derekfountain/zx-spectrum-pico-interface-one/images/case_offset.jpg

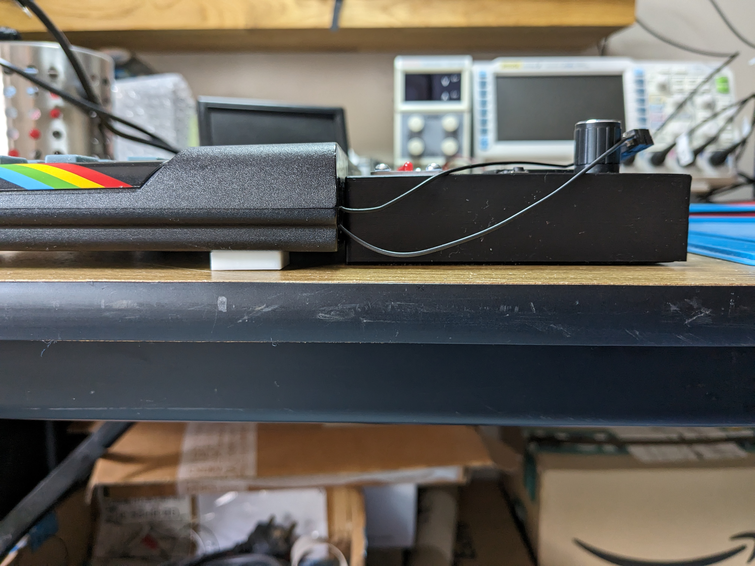
images/case_offset.jpg
