derekfountain/zx-spectrum-pico-interface-one/images/cat1_1633_2_2byte_ins_starts.png

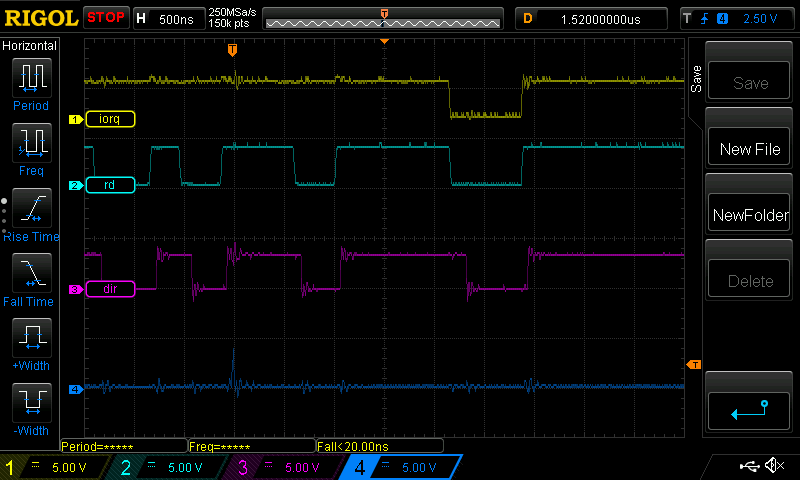
images/cat1_1633_2_2byte_ins_starts.png
