derekfountain/zx-spectrum-pico-interface-one/images/cat1_1633_3_14uSecsbetweenINIRS.png

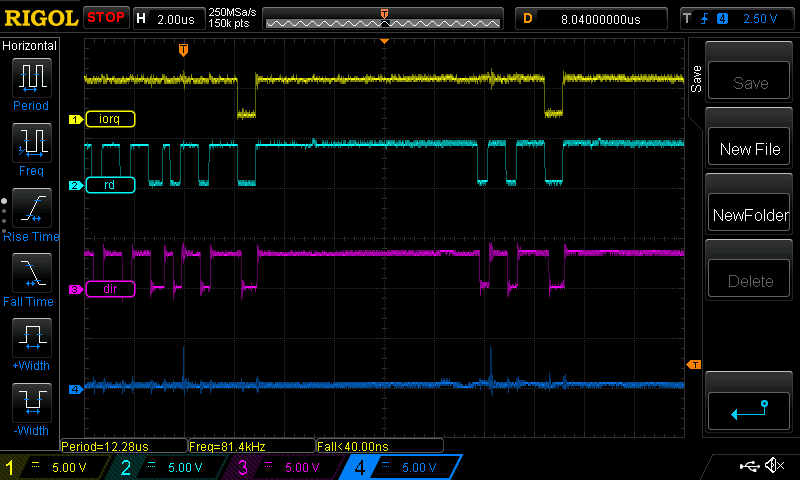
images/cat1_1633_3_14uSecsbetweenINIRS.png
