derekfountain/zx-spectrum-pico-interface-one/images/cat1_1633_4_finalINIR.png

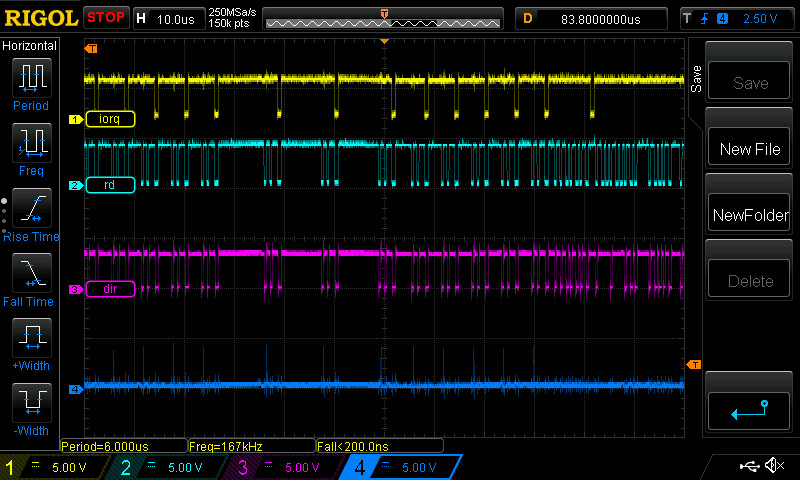
images/cat1_1633_4_finalINIR.png
