derekfountain/zx-spectrum-pico-interface-one/images/cat1_1633_finalOUT.png

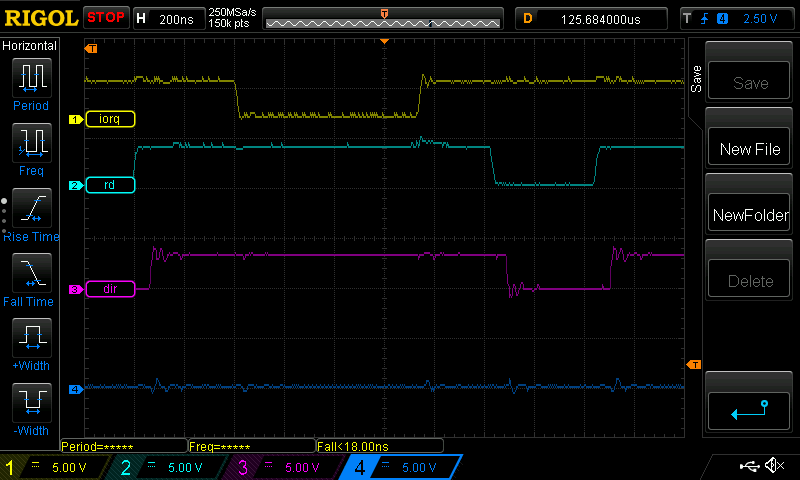
images/cat1_1633_finalOUT.png
