derekfountain/zx-spectrum-pico-interface-one/images/cat1_1633_pastFinalOUT.png

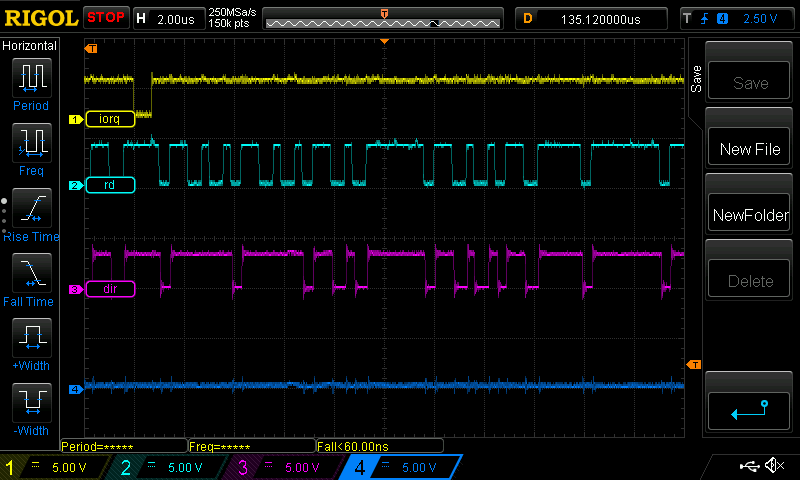
images/cat1_1633_pastFinalOUT.png
