derekfountain/zx-spectrum-pico-interface-one/images/cat1_1633_pastFinalOUTDetail.png

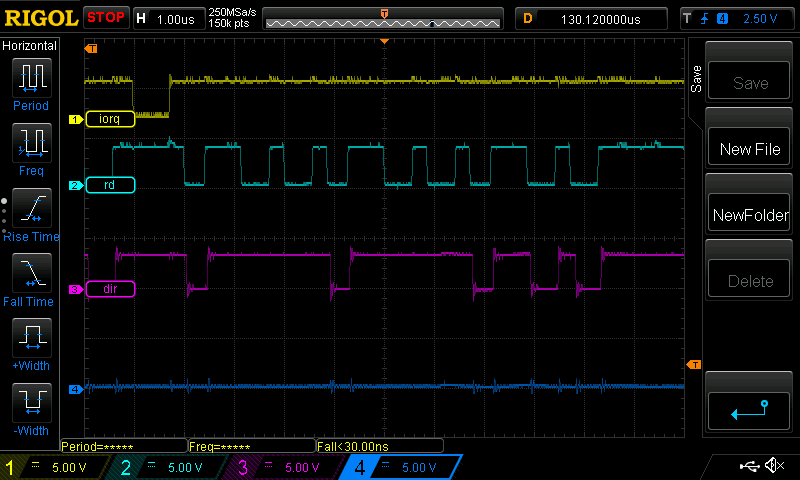
images/cat1_1633_pastFinalOUTDetail.png
