derekfountain/zx-spectrum-pico-interface-one/images/gui_screen.jpg

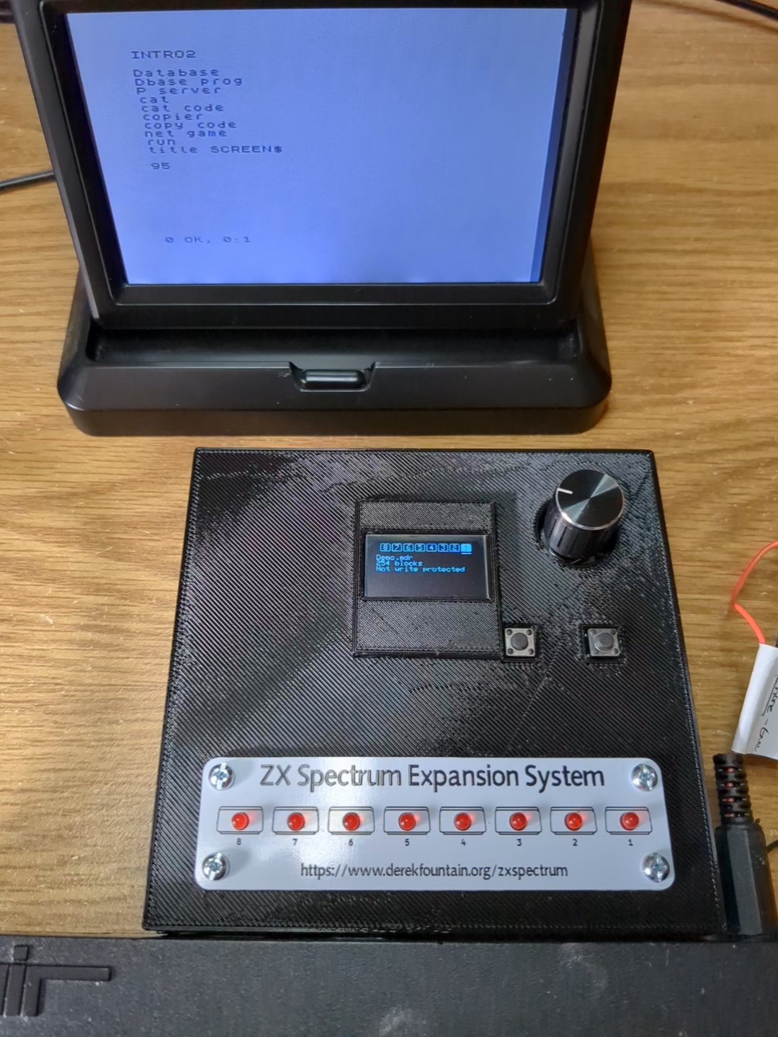
images/gui_screen.jpg
