derekfountain/zx-spectrum-pico-interface-one/images/if1_board_v10.jpg

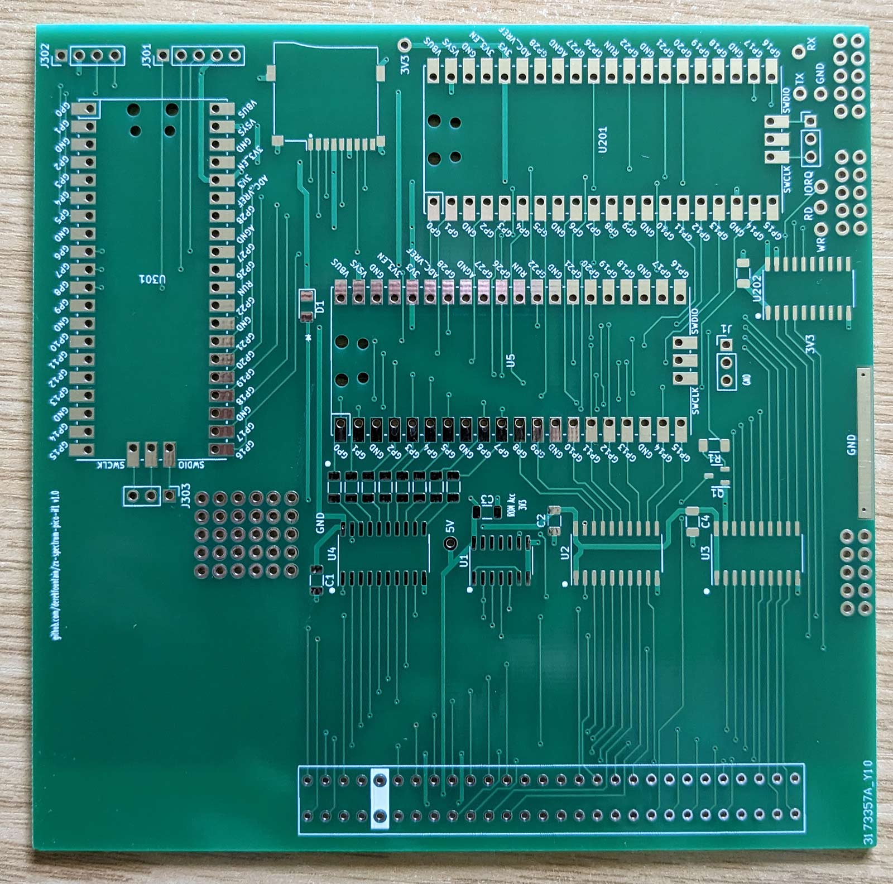
images/if1_board_v10.jpg
