derekfountain/zx-spectrum-pico-interface-one/images/lower_board.jpg

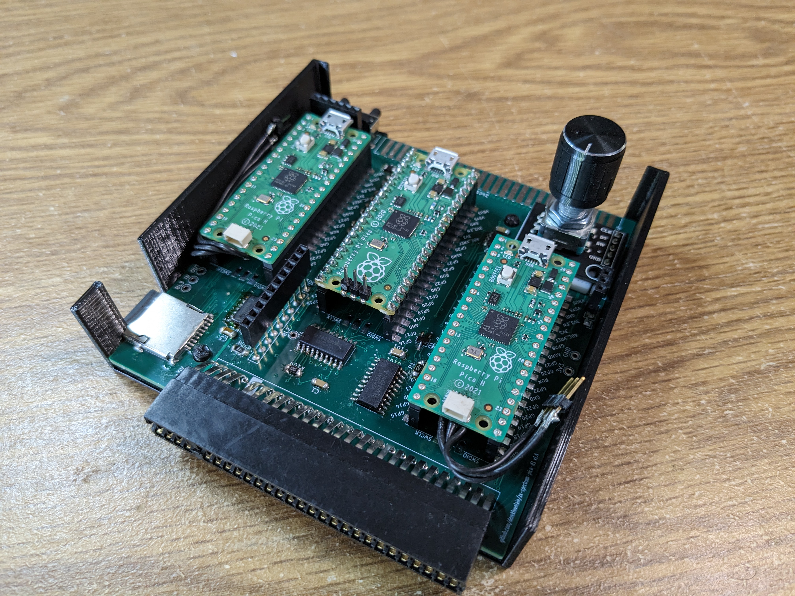
images/lower_board.jpg
