derekfountain/zx-spectrum-pico-interface-one/images/lower_board_rear.jpg

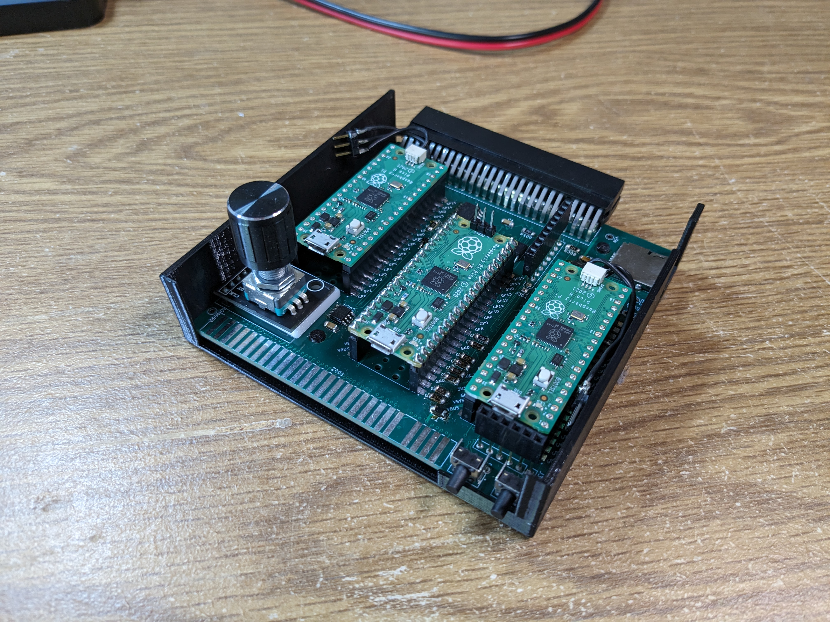
images/lower_board_rear.jpg
