derekfountain/zx-spectrum-pico-interface-one/images/non-working-board.jpg

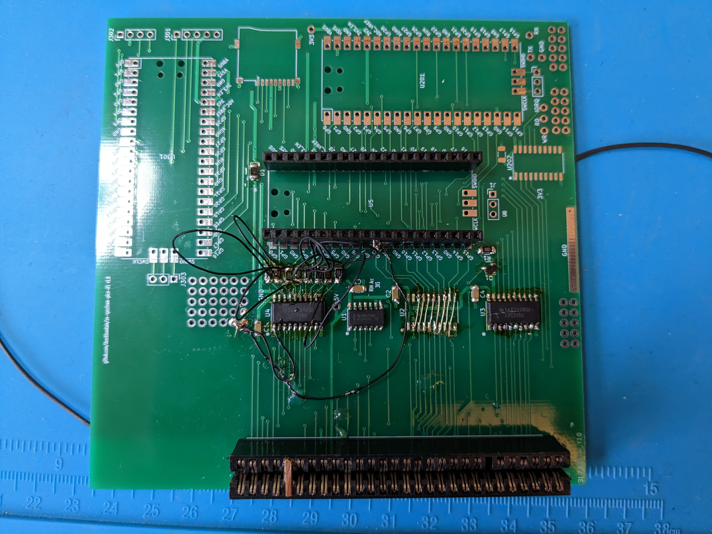
images/non-working-board.jpg
