derekfountain/zx-spectrum-pico-interface-one/images/picos1.jpg

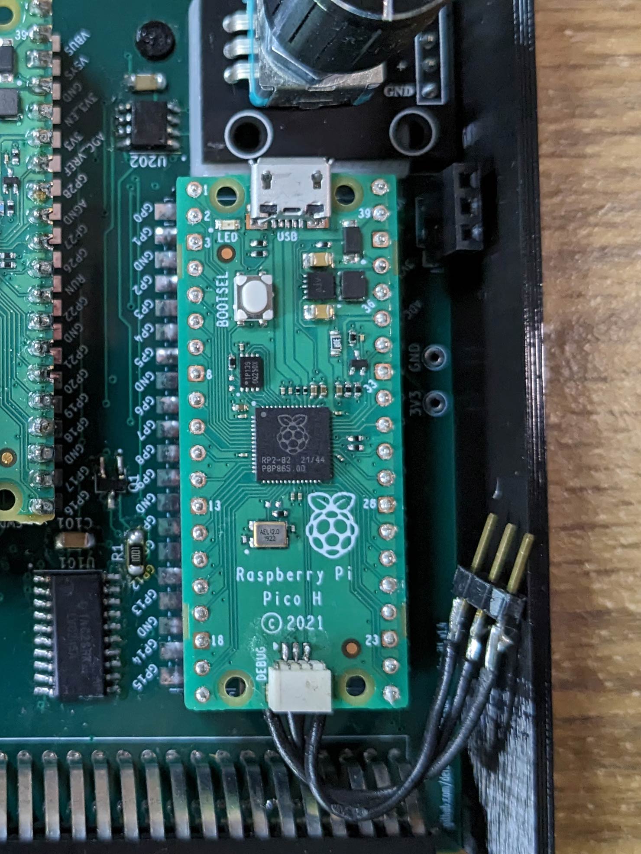
images/picos1.jpg
