derekfountain/zx-spectrum-pico-interface-one/images/picos2.jpg

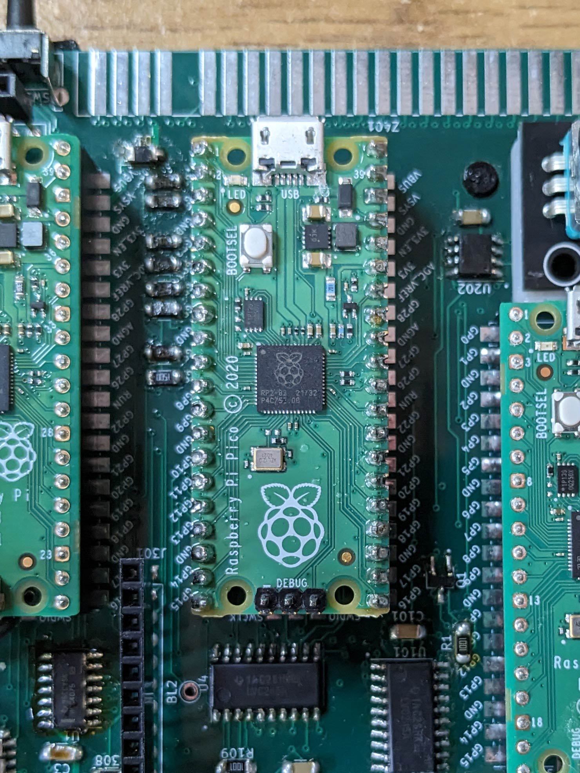
images/picos2.jpg
