derekfountain/zx-spectrum-pico-interface-one/images/picos3.jpg

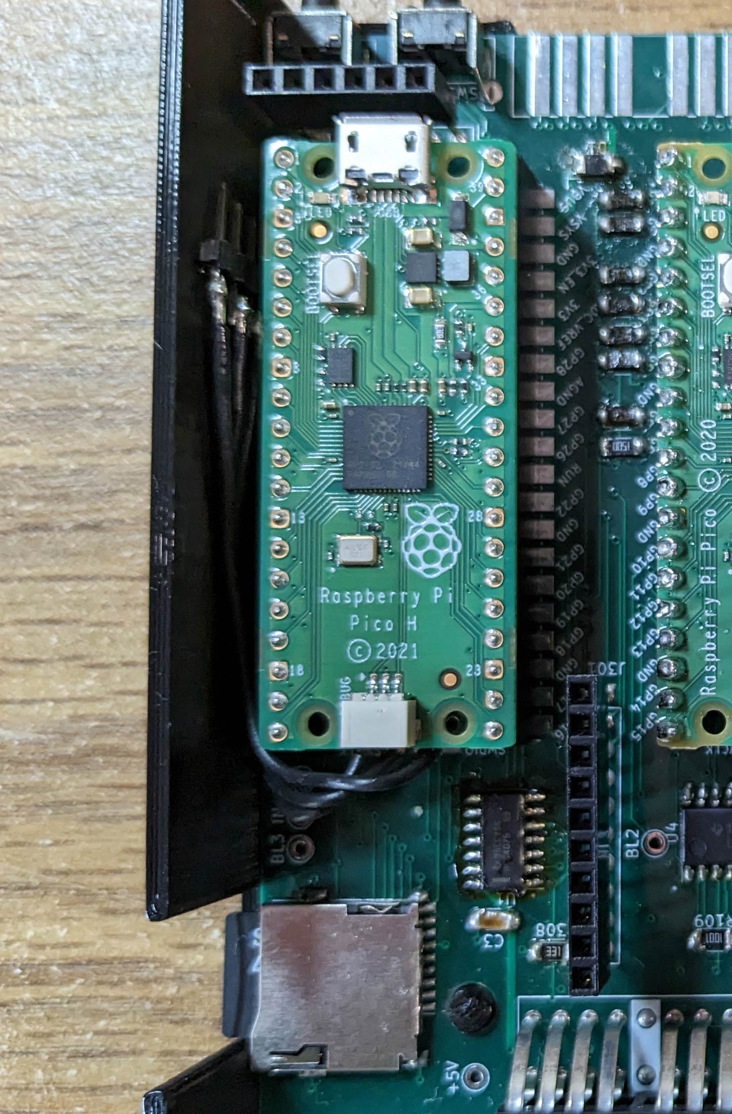
images/picos3.jpg
