derekfountain/zx-spectrum-pico-interface-one/images/pio_io_read.png

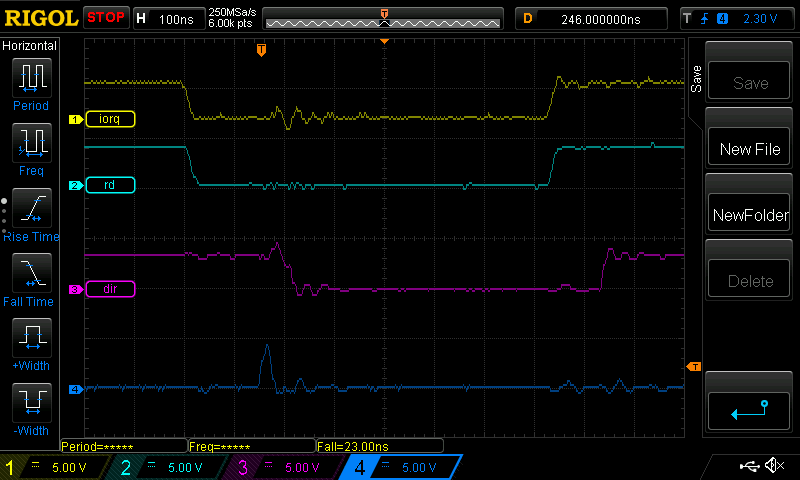
images/pio_io_read.png
