derekfountain/zx-spectrum-pico-interface-one/images/pio_rom_read.png

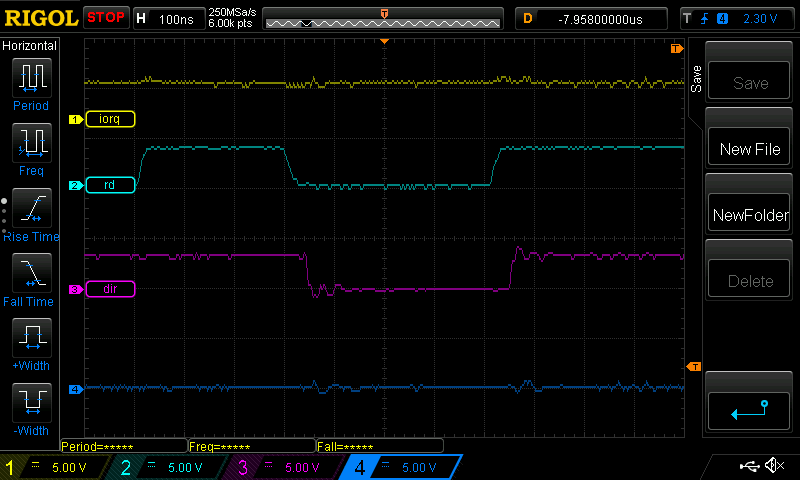
images/pio_rom_read.png
