derekfountain/zx-spectrum-pico-interface-one/images/prototype2_gui.jpg

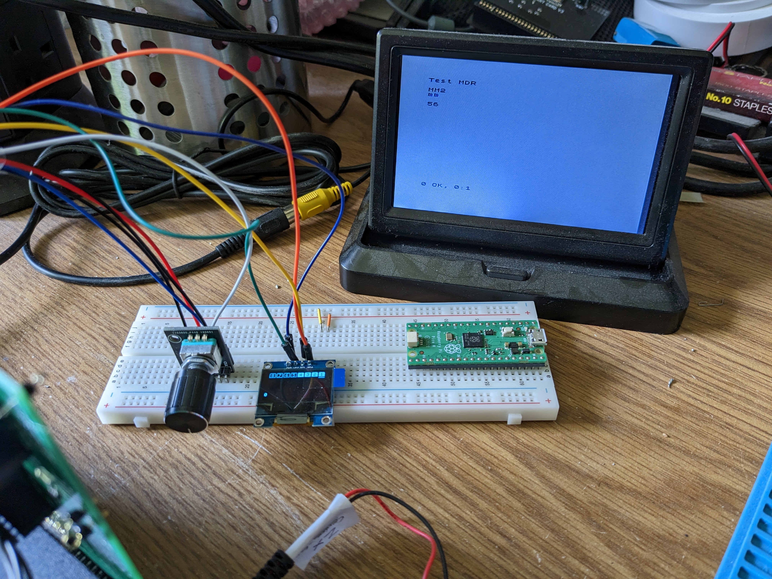
images/prototype2_gui.jpg
