derekfountain/zx-spectrum-pico-interface-one/images/PXL_20230621_114636137.jpg

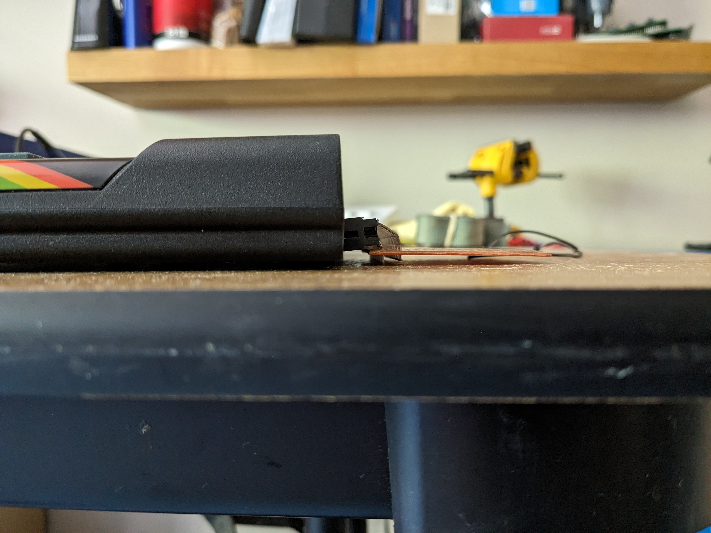
images/PXL_20230621_114636137.jpg
