derekfountain/zx-spectrum-pico-interface-one/images/PXL_20230621_114655089.jpg

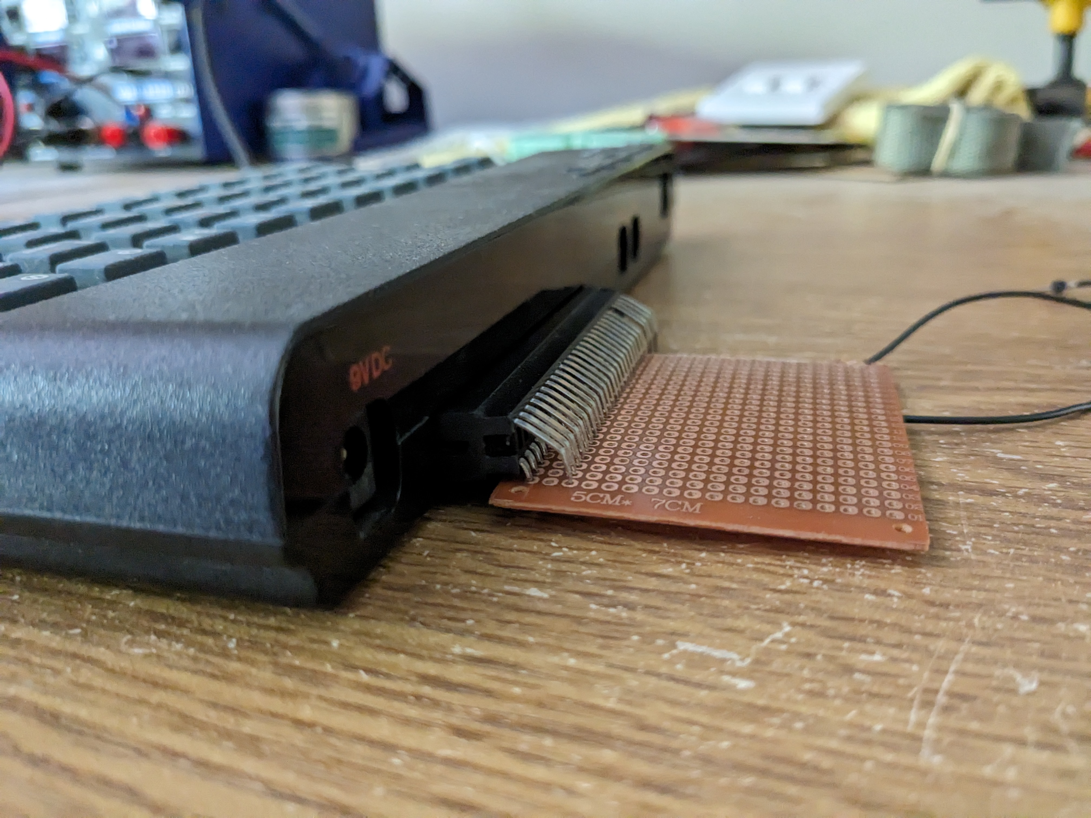
images/PXL_20230621_114655089.jpg
