derekfountain/zx-spectrum-pico-interface-one/images/spi_on_board.jpg

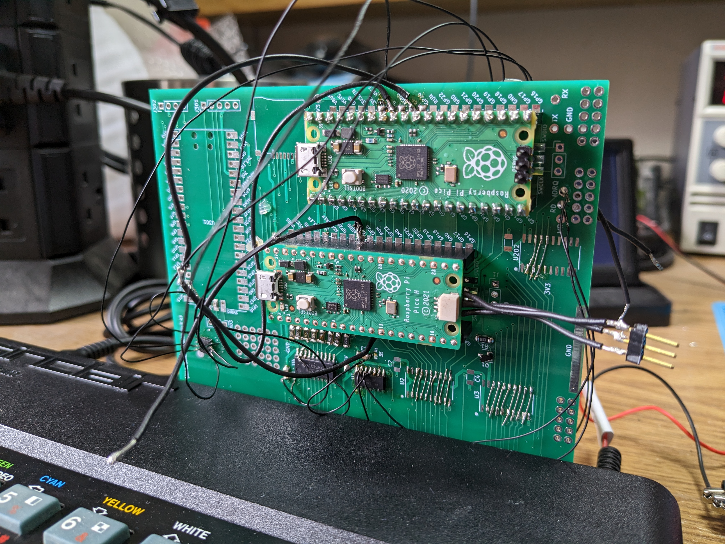
images/spi_on_board.jpg
