derekfountain/zx-spectrum-pico-interface-one/images/spi_ram_prototype.jpg

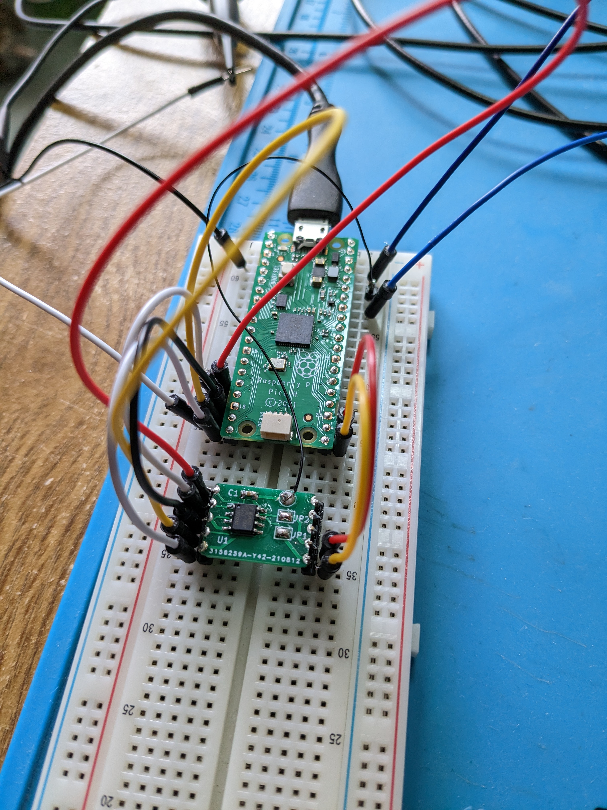
images/spi_ram_prototype.jpg
