derekfountain/zx-spectrum-pico-interface-one/images/spi_read_3us.png

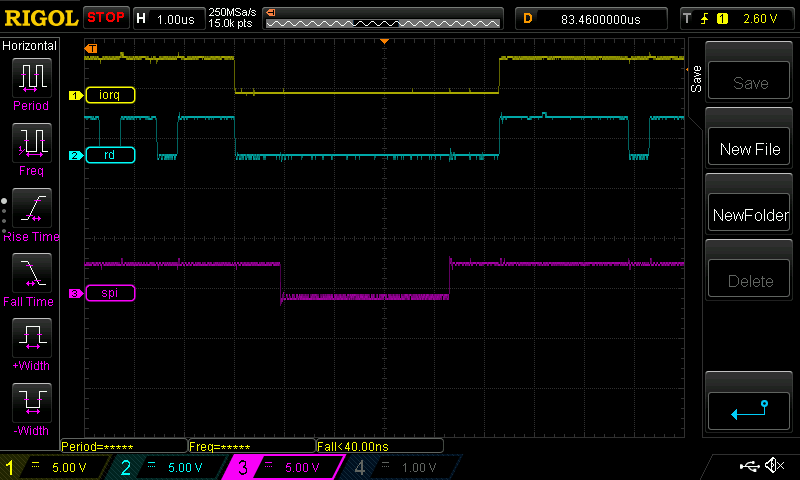
images/spi_read_3us.png
