derekfountain/zx-spectrum-pico-interface-one/images/top_board.jpg

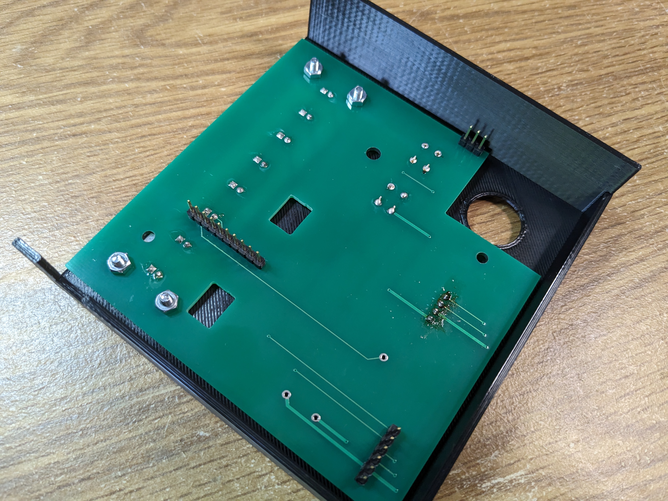
images/top_board.jpg
