derekfountain/zx-spectrum-pico-interface-one/images/trace_first_write_fails_needs_copy_to_ram.png

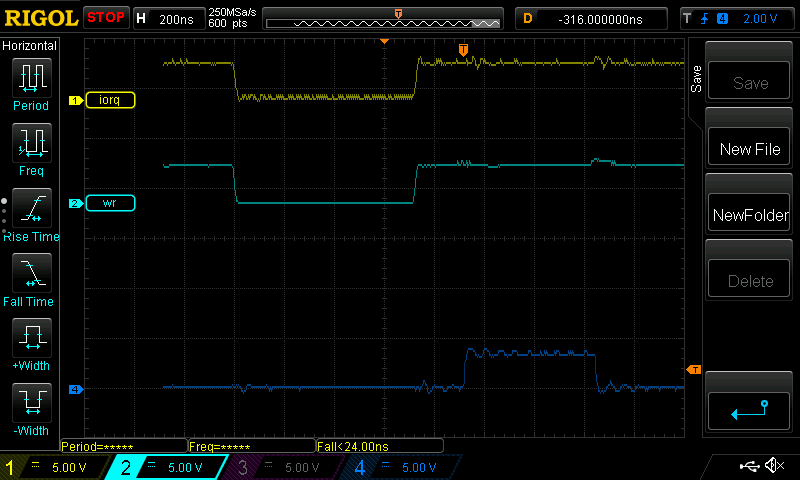
images/trace_first_write_fails_needs_copy_to_ram.png
