derekfountain/zx-spectrum-pico-interface-one/images/trace_second_write_ok.png

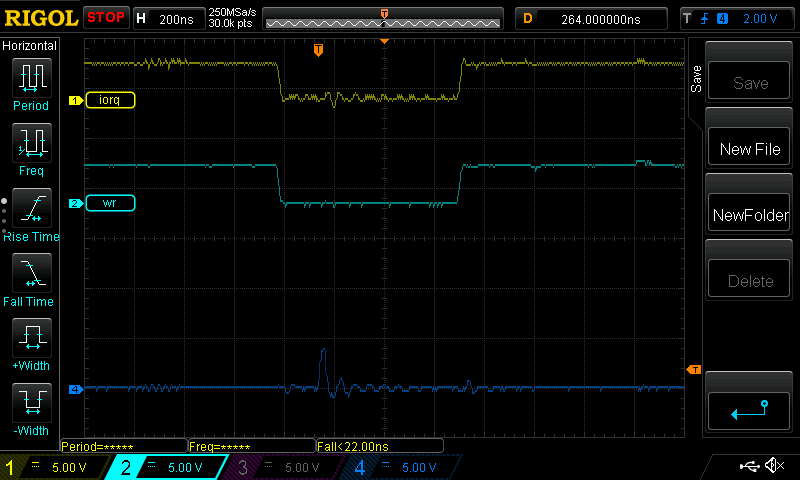
images/trace_second_write_ok.png
