derekfountain/zx-spectrum-pico-interface-one/images/trace_write_e7.png

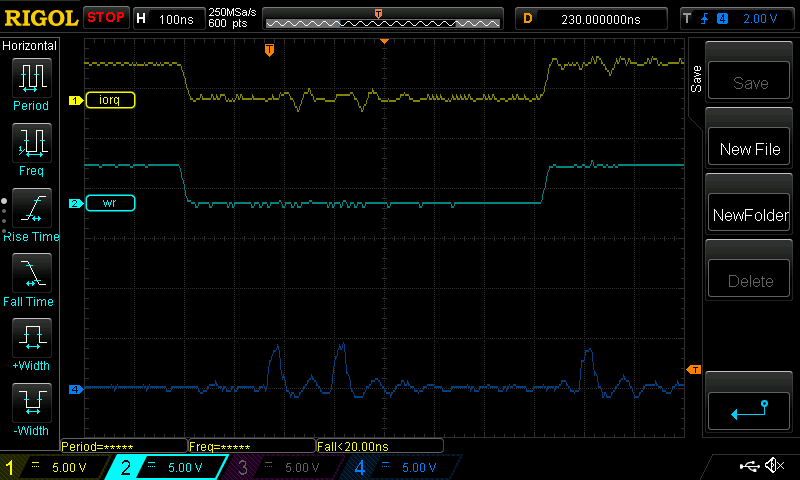
images/trace_write_e7.png
