derekfountain/zx-spectrum-pico-interface-one/images/two_boards.jpg

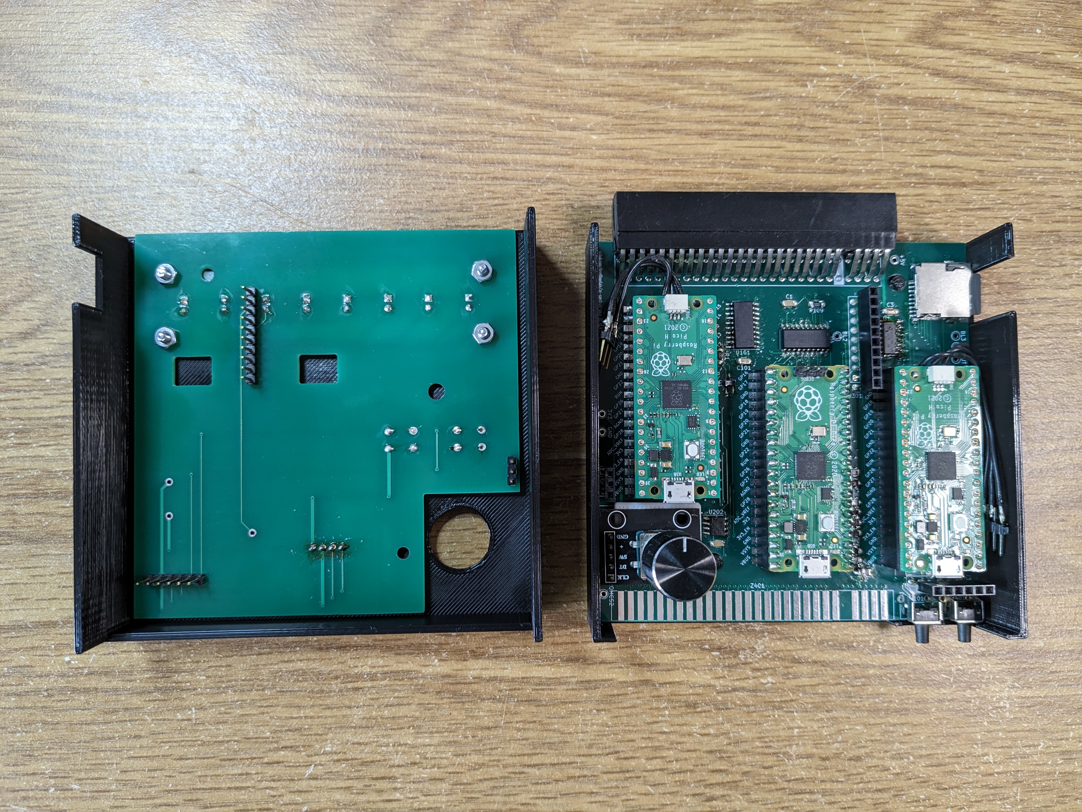
images/two_boards.jpg
