derekfountain/zx-spectrum-pico-interface-one/images/two_picos.jpg

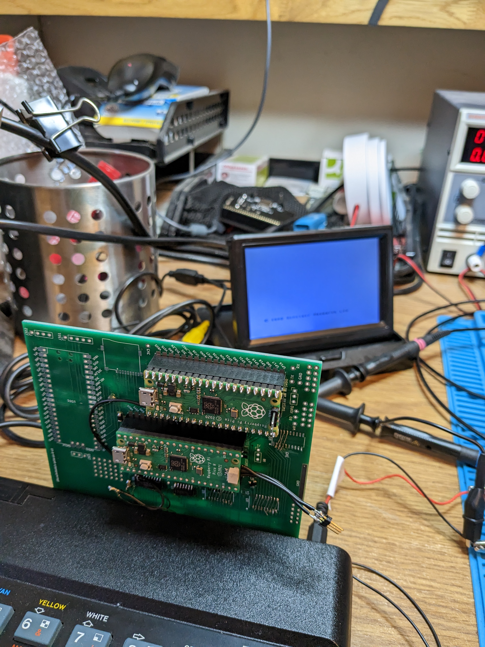
images/two_picos.jpg
