derekfountain/zx-spectrum-pico-interface-one/images/wait_in_read.png

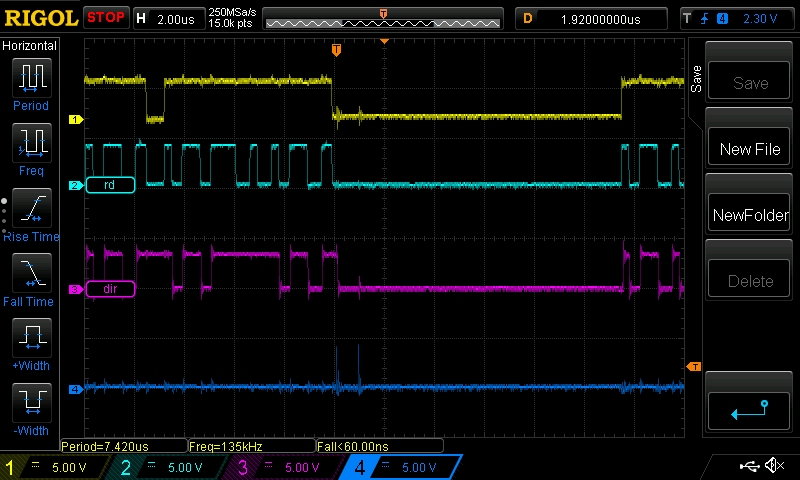
images/wait_in_read.png
