derekfountain/zx-spectrum-pico-interface-one/images/zses_1.jpg

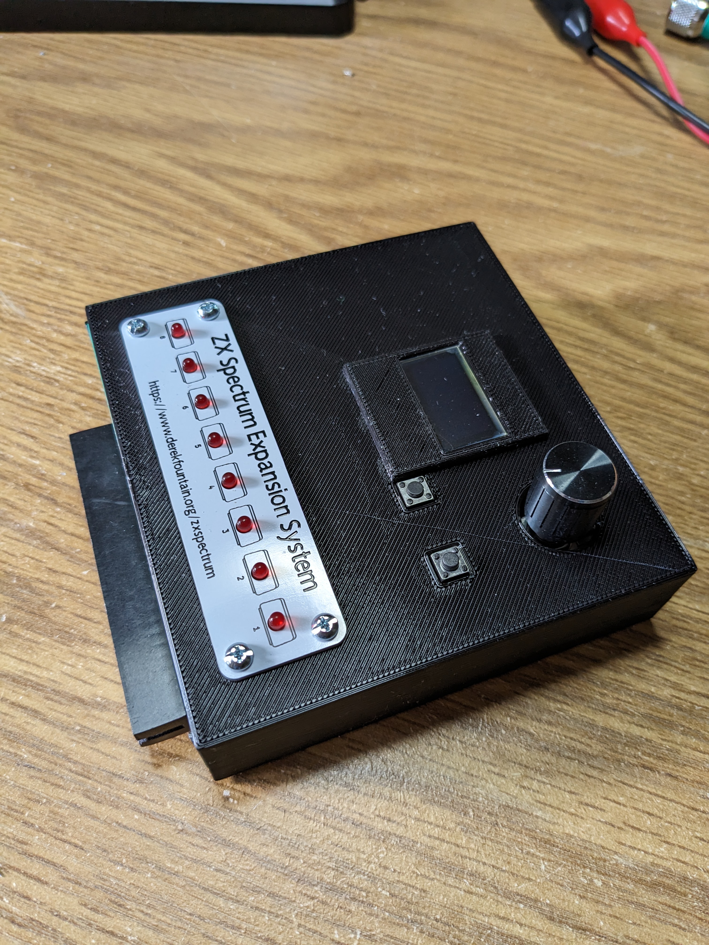
images/zses_1.jpg
