derekfountain/zx-spectrum-pico-interface-one/images/zses_v1_1.jpg

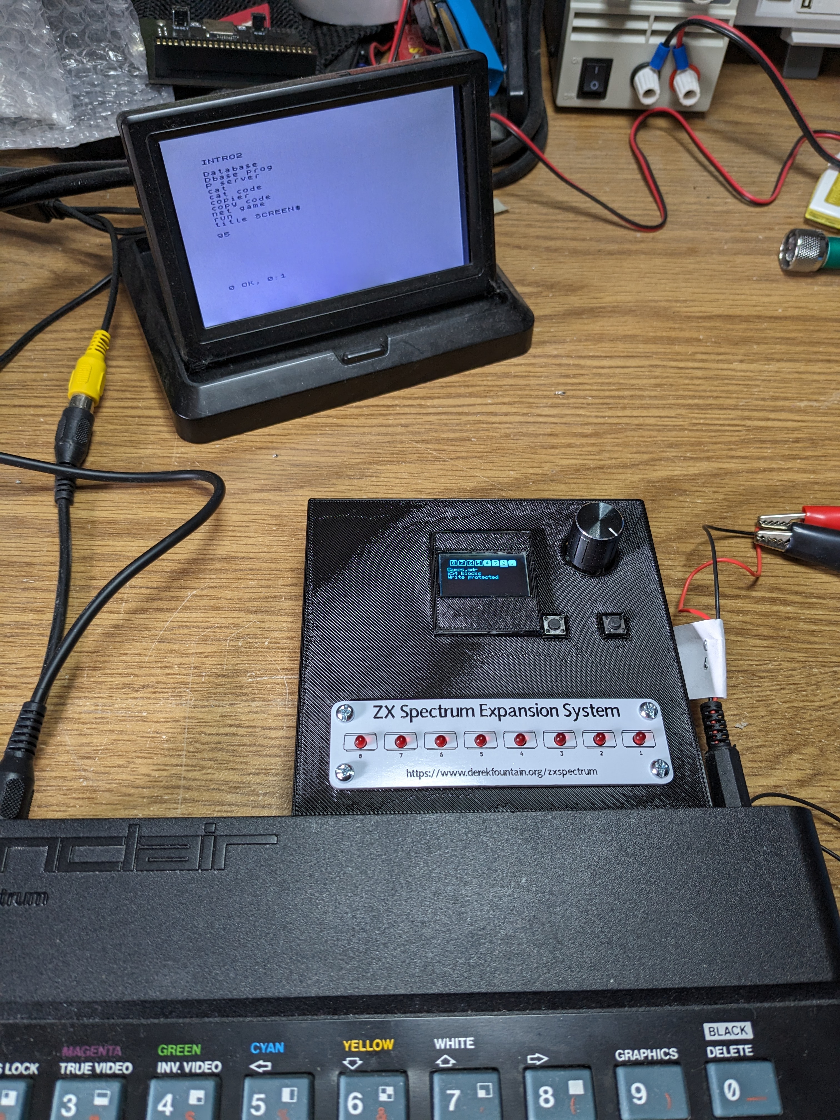
images/zses_v1_1.jpg
