derekfountain/zx-spectrum-pico-interface-one/images/zx_feet_spacers.jpg

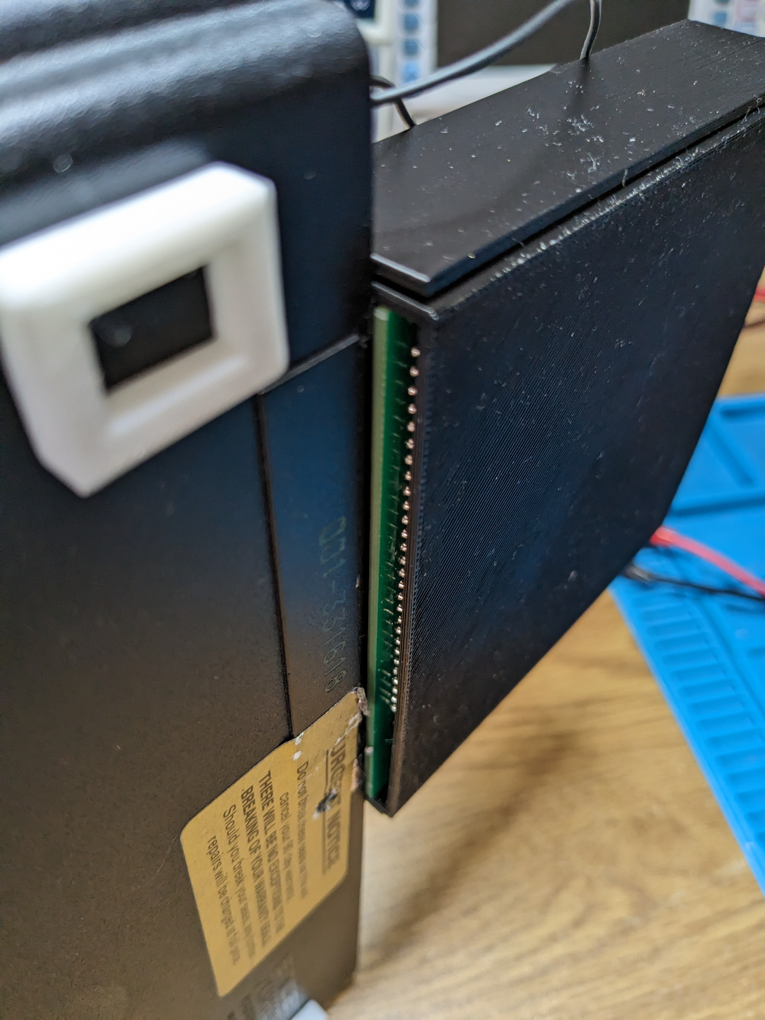
images/zx_feet_spacers.jpg
