derekfountain/zx-spectrum-pico-interface-one/3d_print/pcb_sandwich_spacer/pcb_spacer.scad

cube([20, 18, 4]); 
