derekfountain/zx-spectrum-pico-interface-one/3d_print/top_panel/mII.png

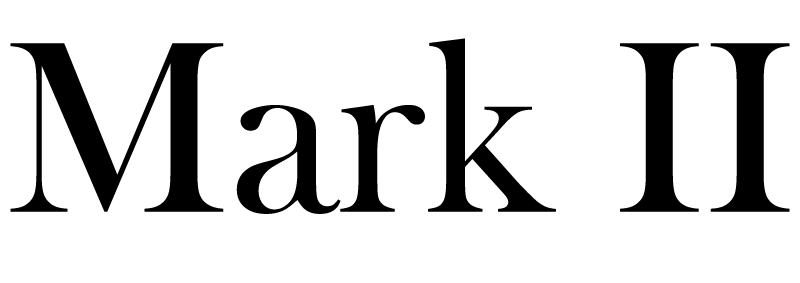
3d_print/top_panel/mII.png
