derekfountain/zx-spectrum-pico-interface-one/images/oled_encoder_wiring_prototype2.jpg

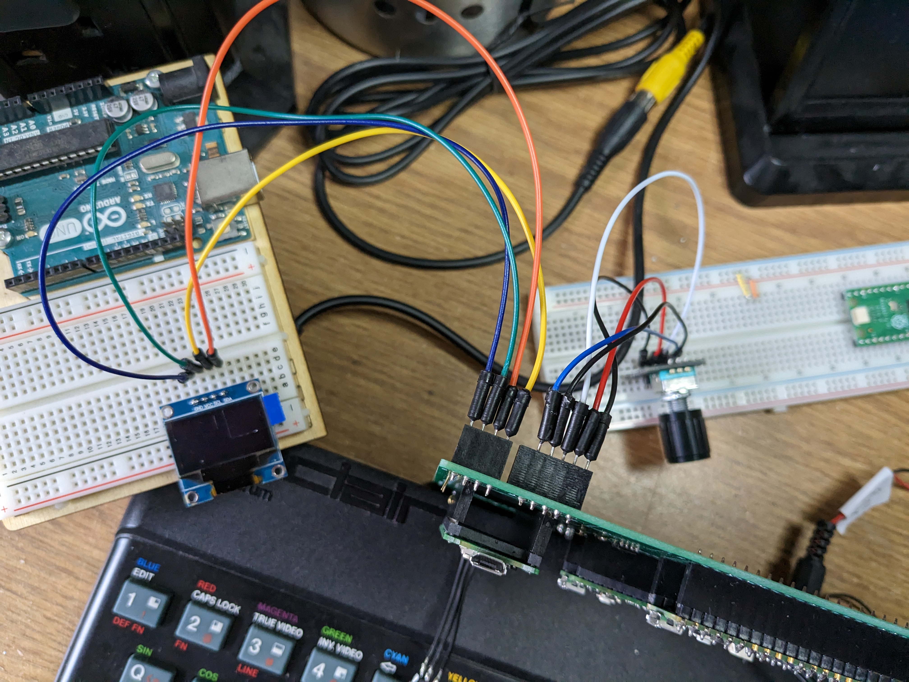
images/oled_encoder_wiring_prototype2.jpg
