derekfountain/zx-spectrum-pico-interface-one/firmware-io/zx_pico_if1_io_fw.c

/*
 * ZX Pico IF1 Firmware, a Raspberry Pi Pico based ZX Interface One emulator
 * Copyright (C) 2023 Derek Fountain
 * 
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
 * You should have received a copy of the GNU General Public License
 * along with this program; if not, write to the Free Software
 * Foundation, Inc., 51 Franklin Street, Fifth Floor, Boston, MA  02110-1301, USA.
 */

/*
 * cmake -DCMAKE_BUILD_TYPE=Debug ..
 * make -j10
 * sudo openocd -f interface/picoprobe.cfg -f target/rp2040.cfg -c "program ./zx_pico_if1_io_fw.elf verify reset exit"
 * sudo openocd -f interface/picoprobe.cfg -f target/rp2040.cfg
 * gdb-multiarch ./zx_pico_if1_io_fw.elf
 *  target remote localhost:3333
 *  load
 *  monitor reset init
 *  continue
 */

#include <stdio.h>
#include <stdint.h>
#include <string.h>
#include <stdlib.h>
#include "pico/stdlib.h"
#include "hardware/gpio.h"
#include "pico/binary_info.h"
#include "pico/multicore.h"
#include "pico/platform.h"
#include "hardware/timer.h"
#include "hardware/spi.h"

#include "if1.h"
#include "spi.h"
#include "ui_io_comms.h"
#include "cartridge.h"

#include "hardware/pio.h"
#include "hardware/clocks.h"
#include "mreq_dir.pio.h"

/* Link to IO Pico is done with transputer based PIO code */
#include "picoputer.pio.h"
#include "link_common.h"

const uint8_t LINKOUT_PIN     = 12;
const uint8_t LINKIN_PIN      = 13;

/* UI to IO Pico link state machines */
static int linkout_sm;
static int linkin_sm;

/* 1 instruction on the 133MHz microprocessor is 7.5ns */
/* 1 instruction on the 140MHz microprocessor is 7.1ns */
/* 1 instruction on the 150MHz microprocessor is 6.6ns */
/* 1 instruction on the 200MHz microprocessor is 5.0ns */

#define OVERCLOCK 150000
//#define OVERCLOCK 270000

const uint8_t LED_PIN = PICO_DEFAULT_LED_PIN;

/*
 * The IF1 port signal comes from the ROM Pico which has can see the
 * address lines. When that's active (low) the Z80 has 0xEF or 0xE7
 * on the lower address lines. The extra bit is A3 which this Pico
 * still needs to be able to see to differentiate them
 */
const uint8_t  IF1_PORT_SIGNAL_GP         = 8;
const uint8_t  A3_GP                      = 9;

const uint32_t IF1_PORT_SIGNAL_BIT_MASK = ((uint32_t)1 <<  IF1_PORT_SIGNAL_GP);
const uint32_t A3_BIT_MASK              = ((uint32_t)1 <<  A3_GP);

const uint8_t  D0_GP        = 0;
const uint8_t  D1_GP        = 1;
const uint8_t  D2_GP        = 2;
const uint8_t  D3_GP        = 3; 
const uint8_t  D4_GP        = 4;
const uint8_t  D5_GP        = 5;
const uint8_t  D6_GP        = 6;
const uint8_t  D7_GP        = 7;

const uint32_t D0_BIT_MASK  = ((uint32_t)1 <<  D0_GP);
const uint32_t D1_BIT_MASK  = ((uint32_t)1 <<  D1_GP);
const uint32_t D2_BIT_MASK  = ((uint32_t)1 <<  D2_GP);
const uint32_t D3_BIT_MASK  = ((uint32_t)1 <<  D3_GP);
const uint32_t D4_BIT_MASK  = ((uint32_t)1 <<  D4_GP);
const uint32_t D5_BIT_MASK  = ((uint32_t)1 <<  D5_GP);
const uint32_t D6_BIT_MASK  = ((uint32_t)1 <<  D6_GP);
const uint32_t D7_BIT_MASK  = ((uint32_t)1 <<  D7_GP);

const uint32_t DBUS_MASK    = ((uint32_t)1 << D0_GP) |
                              ((uint32_t)1 << D1_GP) |
                              ((uint32_t)1 << D2_GP) |
                              ((uint32_t)1 << D3_GP) |
                              ((uint32_t)1 << D4_GP) |
                              ((uint32_t)1 << D5_GP) |
                              ((uint32_t)1 << D6_GP) |
                              ((uint32_t)1 << D7_GP);

/* Input from Z80 indicating an I/O request is happening */
const uint8_t  IORQ_GP                  = 20;
const uint32_t IORQ_BIT_MASK            = ((uint32_t)1 << IORQ_GP);

const uint8_t  RD_GP                    = 21;
const uint32_t RD_BIT_MASK              = ((uint32_t)1 << RD_GP);

const uint8_t  WR_GP                    = 22;
const uint32_t WR_BIT_MASK              = ((uint32_t)1 << WR_GP);

/*
 * These are the bits which allow us to decide whether what is
 * on the Z80 buses is IF1 related
 */
const uint32_t IF1_IOPORT_ACCESS_BIT_MASK = IORQ_BIT_MASK |
                                            RD_BIT_MASK |
                                            WR_BIT_MASK |
                                            IF1_PORT_SIGNAL_BIT_MASK |
                                            A3_BIT_MASK;

const uint32_t PORT_E7_READ =  ((uint32_t)0 << IORQ_GP) |
                               ((uint32_t)0 << RD_GP)   |
                               ((uint32_t)1 << WR_GP)   |
                               ((uint32_t)0 << IF1_PORT_SIGNAL_GP)   |
                               ((uint32_t)0 << A3_GP);

const uint32_t PORT_EF_READ =  ((uint32_t)0 << IORQ_GP) |
                               ((uint32_t)0 << RD_GP)   |
                               ((uint32_t)1 << WR_GP)   |
                               ((uint32_t)0 << IF1_PORT_SIGNAL_GP)   |
                               ((uint32_t)1 << A3_GP);

const uint32_t PORT_E7_WRITE = ((uint32_t)0 << IORQ_GP) |
                               ((uint32_t)1 << RD_GP)   |
                               ((uint32_t)0 << WR_GP)   |
                               ((uint32_t)0 << IF1_PORT_SIGNAL_GP)   |
                               ((uint32_t)0 << A3_GP);

const uint32_t PORT_EF_WRITE = ((uint32_t)0 << IORQ_GP) |
                               ((uint32_t)1 << RD_GP)   |
                               ((uint32_t)0 << WR_GP)   |
                               ((uint32_t)0 << IF1_PORT_SIGNAL_GP)   |
                               ((uint32_t)1 << A3_GP);

/*
 * ROM read logic input, goes 0 when the MREQ to ROM is happening.
 * This is configured as input from the PIO code which is where it's
 * used. It's not used in this C.
 */
const uint8_t  ROM_READ_GP              = 17;
const uint32_t ROM_READ_BIT_MASK        = ((uint32_t)1 << ROM_READ_GP);

/*
 * Data bus level shifter direction pin, 1 is zx->pico, which is the normal
 * position, 0 means pico->zx which is temporarily switched to when the
 * Pico wants to send a data byte back to the Spectrum. This is now unused
 * in this code because the PIO does it, see mreq_dir.pio
 */
const uint8_t  DIR_OUTPUT_GP            = 28;

/*
 * This one's attached to the Z80's /WAIT line, open collector,
 * pull low to set the Z80 waiting
 */
const uint8_t  WAIT_GP                  = 27;

/* Test pin */
const uint8_t  TEST_OUTPUT_GP           = 10;

static void __time_critical_func(blip_test_pin)( void )
{
  gpio_put( TEST_OUTPUT_GP, 1 );
  __asm volatile ("nop");
  __asm volatile ("nop");
  __asm volatile ("nop");
  __asm volatile ("nop");
  gpio_put( TEST_OUTPUT_GP, 0 );
  __asm volatile ("nop");
  __asm volatile ("nop");
  __asm volatile ("nop");
  __asm volatile ("nop");
}

/*
 * Rudimentary trace table for whole program
 *
 * (gdb) set print repeats 0
 * (gdb) set print elements unlimited
 * (gdb) set pagination off
 * (gdb) set max-value-size unlimited
 * (gdb) p trace_table
 */
static TRACE_TYPE trace_table[NUM_TRACE_ENTRIES];
static uint8_t  trace_active=1;
static uint32_t trace_index=0;

void trace( TRACE_CODE code, uint32_t data )
{
  if( trace_active )
  {
    trace_table[trace_index].i=trace_index;
    trace_table[trace_index].code=code;
    trace_table[trace_index].data=data;

    if( ++trace_index == NUM_TRACE_ENTRIES )
      trace_index=0;
  }
}

/*
 * This PIO state machine is used to change the data bus level
 * shifter direction when either the ROM handling Pico says it
 * wants to send a byte back to the ZX, or when this code wants
 * to send a byte from the IF1 back to the ZX.
 */
static PIO pio;
static uint sm_mreq;

/*
 * Mutex to protect the PSRAM SPI device from concurrent access.
 * I can't have the Z80 IO reads and writes getting mixed up with the
 * GUI functions of inserting and saving cartride data which is
 * on the PSRAM.
 */
auto_init_mutex( psram_mutex );

/* Each microdrive's error status as far as this code is concerned */
static cartridge_error_t cartridge_error_status[NUM_MICRODRIVES];

/*
 * I/O port handling runs in the second core.
 */
static uint8_t core1_running = 0;
void __time_critical_func(core1_main)( void )
{
  /* All interrupts off in this core, the IO emulation won't work with interrupts enabled */
  irq_set_mask_enabled( 0xFFFFFFFF, 0 );  

  trace(TRC_INTS_OFF, 0);

  /* Set up the IF1 structures */
  if1_init();

  trace(TRC_IF1_INIT, 0);

  /* Tracing off, I'll turn it back on if I get a bug where it's needed */
  trace_active=0;

  /* Signal to other core we're up and running */
  core1_running = 1;
  while( 1 )
  {
    register uint32_t gpios_state = gpio_get_all();

    if( (gpios_state & IF1_IOPORT_ACCESS_BIT_MASK) == PORT_E7_WRITE )
    {
      /* Z80 write (OUT instruction) to port 0xE7 (231), microdrive data */

      /* Pick up the pattern of bits from the data bus GPIOs */
      register uint32_t z80_written_byte = (gpios_state & DBUS_MASK);

      /* Set Z80 waiting */
      gpio_set_dir(WAIT_GP, GPIO_OUT);
      gpio_put(WAIT_GP, 0);

      /* Writing to PSRAM, critical section */
      mutex_enter_blocking( &psram_mutex );

      // trace(TRC_WRITE_E7_DATA, z80_written_byte);

      /* Write the byte out */
      port_mdr_out( z80_written_byte );

      /* Done waiting */
      gpio_set_dir(WAIT_GP, GPIO_IN);

      mutex_exit( &psram_mutex );

      /* Wait for the IO request to complete */
      while( (gpio_get_all() & IORQ_BIT_MASK) == 0 );
    }

    else if( (gpios_state & IF1_IOPORT_ACCESS_BIT_MASK) == PORT_EF_WRITE )
    {
      /* Z80 write (OUT instruction) to port 0xEF (239), microdrive control */
      /* This turns on the motor */

      /* Pick up the pattern of bits from the data bus GPIOs */
      register uint32_t control_byte = (gpios_state & DBUS_MASK);
    
      /* Set Z80 waiting */
      gpio_set_dir(WAIT_GP, GPIO_OUT);
      gpio_put(WAIT_GP, 0);

      // trace(TRC_WRITE_EF_CONTROL, control_byte);

      /* Microdrive control, motor switch */
      port_ctr_out( control_byte );

      /* Done waiting */
      gpio_set_dir(WAIT_GP, GPIO_IN);

      /* Wait for the IO request to complete */
      while( (gpio_get_all() & IORQ_BIT_MASK) == 0 );
    }

    else if( (gpios_state & IF1_IOPORT_ACCESS_BIT_MASK) == PORT_E7_READ )
    {
      /* Z80 read from port 0xE7 (231), Z80 wants a microdrive data byte */

      /* Set Z80 waiting */
      gpio_set_dir(WAIT_GP, GPIO_OUT);
      gpio_put(WAIT_GP, 0);

      /* Reading from PSRAM, critical section */
      mutex_enter_blocking( &psram_mutex );

      /* Direction needs to be Pico->ZX */
      pio_sm_put( pio, sm_mreq, 1 );

      /* Make data bus GPIOs outputs, pointed at the ZX */
      gpio_set_dir_out_masked( DBUS_MASK );

      /* Port handling function returns the data from the microdrive */
      register uint32_t md_data = port_mdr_in();
      gpio_put_masked( DBUS_MASK, md_data );

      // trace(TRC_READ_E7_DATA, md_data);

      mutex_exit( &psram_mutex );

      /* Done waiting */
      gpio_set_dir(WAIT_GP, GPIO_IN);

      /* Wait for the IO request to complete */
      while( (gpio_get_all() & IORQ_BIT_MASK) == 0 );

      /* Make the GPIOs inputs again */
      gpio_set_dir_in_masked( DBUS_MASK );
          
      /* Put level shifter direction back to ZX->Pico */
      pio_sm_put( pio, sm_mreq, 0 );
    }

    else if( (gpios_state & IF1_IOPORT_ACCESS_BIT_MASK) == PORT_EF_READ )
    {
      /* Z80 read from port 0xEF (239), microdrive status */

      /* Set Z80 waiting */
      gpio_set_dir(WAIT_GP, GPIO_OUT);
      gpio_put(WAIT_GP, 0);

      /* Direction needs to be Pico->ZX */
      pio_sm_put( pio, sm_mreq, 1 );

      /* Make data bus GPIOs outputs, pointed at the ZX */
      gpio_set_dir_out_masked( DBUS_MASK );

      /* Port handling function returns the status */
      register uint32_t md_status = port_ctr_in();
      gpio_put_masked( DBUS_MASK, md_status );

      // trace(TRC_READ_EF_STATUS, md_status);

      /* Done waiting */
      gpio_set_dir(WAIT_GP, GPIO_IN);

      /* Wait for the IO request to complete */
      while( (gpio_get_all() & IORQ_BIT_MASK) == 0 );

      /* Make the GPIOs inputs again */
      gpio_set_dir_in_masked( DBUS_MASK );
          
      /* Put level shifter direction back to ZX->Pico */
      pio_sm_put( pio, sm_mreq, 0 );
    }
  } 
}


/*
 * Write a block of data into the pseudo RAM device at a given location.
 */
static void write_psram_block( uint32_t psram_offset, uint8_t *block_buffer, uint32_t length )
{
  /* Writing to PSRAM, critical section */
  mutex_enter_blocking( &psram_mutex );

  gpio_put( PSRAM_SPI_CSN_PIN, 0 );

  uint8_t write_cmd[] = { PSRAM_CMD_WRITE,
                          psram_offset >> 16, psram_offset >> 8, psram_offset 
                        };

  spi_write_blocking(PSRAM_SPI, write_cmd,    sizeof(write_cmd));
  spi_write_blocking(PSRAM_SPI, block_buffer, length);

  gpio_put( PSRAM_SPI_CSN_PIN, 1 );

  mutex_exit( &psram_mutex );

  return;
}


/*
 * Read a block of data from pseudo RAM device
 */
static void read_psram_block( uint32_t psram_offset, uint8_t *block_buffer, uint32_t length )
{
  /* Reading from PSRAM, critical section */
  mutex_enter_blocking( &psram_mutex );

  gpio_put( PSRAM_SPI_CSN_PIN, 0 );

  uint8_t read_cmd[] = { PSRAM_CMD_READ,
			 psram_offset >> 16, psram_offset >> 8, psram_offset };
  spi_write_blocking(PSRAM_SPI, read_cmd, sizeof(read_cmd));

  spi_read_blocking(PSRAM_SPI, 0, block_buffer, length ); 

  gpio_put( PSRAM_SPI_CSN_PIN, 1 );

  mutex_exit( &psram_mutex );

  return;
}


/*
 * Receive and return a command from the UI Pico. This waits for and sorts
 * out the preamble, then returns the command byte.
 *
 * It doesn't time out. If this code is being called it's assumed that the
 * core is waiting for a command and has nothing else to do. So it'll
 * wait forever, bypassing anything which doesn't look like a command
 * sequence.
 */
static UI_TO_IO_CMD get_ui_to_io_cmd( void )
{
  uint8_t preamble[] = UI_TO_IO_CMD_PREAMBLE;

  uint8_t preamble_received = 0;

  uint8_t preamble_index = 0;

  /*
   * This makes an effort at spotting the preamble of a command byte.
   * The premable is a handful of bytes which are easy to see on a 
   * scope, followed by a command byte. If the sequence happens to
   * exist in a stream of cartridge data which might be being sent
   * over then this won't help, but in most cases it might sort
   * things out when the UI pico gets restarted.
   */
  while( ! preamble_received )
  {
    uint8_t received_byte;
    while( ui_link_receive_acked_byte( pio1, linkin_sm, linkout_sm, &received_byte ) != LINK_BYTE_DATA );

    if( received_byte != preamble[preamble_index] )
    {
      if( preamble_index == 0 )
      {
	continue;
      }
      else
      {
	if( received_byte != preamble[0] )
	{
	  preamble_index = 0;
	  continue;
	}
	else
	{
	  /*
	   * Byte matches the first of the preamble sequence. It could be
	   * the start of the preamble. Run with it from here.
	   */
	}
      }
    }

    if( ++preamble_index == sizeof(preamble) )
    {
      preamble_received = 1;
    }
  }

  uint8_t received_byte;
  while( ui_link_receive_acked_byte( pio1, linkin_sm, linkout_sm, &received_byte ) != LINK_BYTE_DATA );
  return received_byte;
}


/*
 * Send an ACK back to the UI Pico.
 */
void send_ack_to_ui( void )
{
  ui_link_send_byte( pio1, linkout_sm, linkin_sm, UI_TO_IO_ACK );

  return;
}


int __time_critical_func(main)( void )
{
  bi_decl(bi_program_description("ZX Spectrum Pico IF1 board binary."));

  /* Clean out the trace table */
  memset( trace_table, 0, sizeof(trace_table) );

  /* All interrupts off */
  irq_set_mask_enabled( 0xFFFFFFFF, 0 );  

#ifdef OVERCLOCK
  set_sys_clock_khz( OVERCLOCK, 1 );
#endif

  for( uint8_t microdrive_index = 0; microdrive_index < NUM_MICRODRIVES; microdrive_index++ )
  {
    cartridge_error_status[microdrive_index] = CARTRIDGE_ERR_OK;
  }

  trace(TRC_DATA_CONV,0 );

  /* Pull the buses to zeroes. Most of the address bus info comes from the ROM Pico */
  gpio_init( IF1_PORT_SIGNAL_GP  ); gpio_set_dir( IF1_PORT_SIGNAL_GP,  GPIO_IN );
  gpio_init( A3_GP  ); gpio_set_dir( A3_GP,  GPIO_IN );  gpio_pull_down( A3_GP  );

  gpio_init( D0_GP  ); gpio_set_dir( D0_GP,  GPIO_IN );  gpio_pull_down( D0_GP  );
  gpio_init( D1_GP  ); gpio_set_dir( D1_GP,  GPIO_IN );  gpio_pull_down( D1_GP  );
  gpio_init( D2_GP  ); gpio_set_dir( D2_GP,  GPIO_IN );  gpio_pull_down( D2_GP  );
  gpio_init( D3_GP  ); gpio_set_dir( D3_GP,  GPIO_IN );  gpio_pull_down( D3_GP  );
  gpio_init( D4_GP  ); gpio_set_dir( D4_GP,  GPIO_IN );  gpio_pull_down( D4_GP  );
  gpio_init( D5_GP  ); gpio_set_dir( D5_GP,  GPIO_IN );  gpio_pull_down( D5_GP  );
  gpio_init( D6_GP  ); gpio_set_dir( D6_GP,  GPIO_IN );  gpio_pull_down( D6_GP  );
  gpio_init( D7_GP  ); gpio_set_dir( D7_GP,  GPIO_IN );  gpio_pull_down( D7_GP  );

  gpio_init( IORQ_GP ); gpio_set_dir( IORQ_GP, GPIO_IN );
  gpio_pull_up( IORQ_GP );

  gpio_init( RD_GP ); gpio_set_dir( RD_GP, GPIO_IN );
  gpio_pull_up( RD_GP );

  gpio_init( WR_GP ); gpio_set_dir( WR_GP, GPIO_IN );
  gpio_pull_up( WR_GP );

  /*
   * Wait is an output from here to the Z80. Set as an input to sink the +5V
   * that's on it when it's not being used.
   */
  gpio_init( WAIT_GP ); gpio_set_dir( WAIT_GP, GPIO_IN );

  gpio_init( LED_PIN ); gpio_set_dir( LED_PIN, GPIO_OUT );

  trace(TRC_GPIOS_INIT ,0);

  /* Use PIO to switch the level shifter's DIRection */
  pio              = pio0;
  sm_mreq          = pio_claim_unused_sm( pio, true );
  uint offset_mreq = pio_add_program( pio, &mreq_dir_program );
  mreq_dir_program_init( pio, sm_mreq, offset_mreq, ROM_READ_GP, DIR_OUTPUT_GP );
  pio_sm_set_enabled(pio, sm_mreq, true);

  trace(TRC_PIOS_INIT, 0);

  /*
   * Psuedo SRAM device, on SPI
   *
   * Enable SPI 0 at <n> MHz and connect to GPIOs. Might as well ask for the theoretical maximum.
   */
  mutex_init( &psram_mutex );
  mutex_enter_blocking( &psram_mutex );
  spi_init(PSRAM_SPI, 62 * 1000 * 1000);
  gpio_set_function(PSRAM_SPI_RX_PIN, GPIO_FUNC_SPI);
  gpio_set_function(PSRAM_SPI_SCK_PIN, GPIO_FUNC_SPI);
  gpio_set_function(PSRAM_SPI_TX_PIN, GPIO_FUNC_SPI);

  /*
   * With reference to this thread:
   *  https://forums.raspberrypi.com//viewtopic.php?f=145&t=300589
   * this PSRAM device likes its slave-select line low across the
   * whole transaction (not high and low, byte to byte). It's
   * therefore controlled with software.
   */
  gpio_init(PSRAM_SPI_CSN_PIN);
  gpio_set_dir(PSRAM_SPI_CSN_PIN, GPIO_OUT);
  gpio_put(PSRAM_SPI_CSN_PIN, 1);

  /* Datasheet says 150uS between power up and the reset command */
  busy_wait_us_32(200);

  /* All examples I've seen don't bother with this reset, might be optional */
  uint8_t reset_cmd[] = { PSRAM_CMD_RESET_ENABLE, 
                          PSRAM_CMD_RESET };
  gpio_put(PSRAM_SPI_CSN_PIN, 0); 
  spi_write_blocking(PSRAM_SPI, reset_cmd, 2);
  gpio_put(PSRAM_SPI_CSN_PIN, 1);   

  /* Test SPI RAM is present */
  gpio_put(PSRAM_SPI_CSN_PIN, 0);

  /* Read ID, on the chip I'm using takes 0x9F as the command followed by 3 "don't care"s */
  uint8_t read_cmd[] = { PSRAM_CMD_READ_ID,
                         0, 0, 0 };
  spi_write_blocking(PSRAM_SPI, read_cmd, sizeof(read_cmd)); 
                        
  /* Chip I'm using returns 0x0D, 0x5D according to the datasheet */
  uint8_t id1, id2;
  spi_read_blocking(PSRAM_SPI, 0, &id1, 1 ); 
  spi_read_blocking(PSRAM_SPI, 0, &id2, 1 ); 
  gpio_put(PSRAM_SPI_CSN_PIN, 1);

  if( (id1 != 0x0D) || (id2 != 0x5D) )
  {
// Send an error to the UI here, not sure what it can do with it though
    while(1)
    {
      gpio_put(LED_PIN, 1);
      busy_wait_us_32(1000000);
      gpio_put(LED_PIN, 0);
      busy_wait_us_32(100000);
    }
  }

  mutex_exit( &psram_mutex );

  trace(TRC_SPI_INIT, 0);

  /*
   * Set up the link to the UI Pico. This uses a pair of PIO programs to send and receive
   * over an asynchronous, 2 wire link. See https://github.com/derekfountain/pico-pio-connect
   */

  /* Outbound link, to UI Pico */
  gpio_init(LINKOUT_PIN); gpio_set_dir(LINKOUT_PIN,GPIO_OUT); gpio_put(LINKOUT_PIN, 1);
  gpio_set_function(LINKOUT_PIN, GPIO_FUNC_PIO1);

  linkout_sm      = pio_claim_unused_sm(pio1, true);
  uint offset     = pio_add_program(pio1, &picoputerlinkout_program);
  picoputerlinkout_program_init(pio1, linkout_sm, offset, LINKOUT_PIN);

  /* Inbound link, from IO Pico */
  gpio_init(LINKIN_PIN); gpio_set_dir(LINKIN_PIN,GPIO_IN);
  gpio_set_function(LINKIN_PIN, GPIO_FUNC_PIO1);
    
  linkin_sm       = pio_claim_unused_sm(pio1, true);
  offset          = pio_add_program(pio1, &picoputerlinkin_program);
  picoputerlinkin_program_init(pio1, linkin_sm, offset, LINKIN_PIN);

  /*
   * This Pico comes up second, the IO Pico will be waiting for the response
   * to its initialisation sequence. Send it immediately.
   */
  ui_link_wait_for_init_sequence( pio1, linkin_sm, linkout_sm );

  trace(TRC_LINK_INIT, 0);

  /* Test pin, blips the scope */
  gpio_init(TEST_OUTPUT_GP); gpio_set_dir(TEST_OUTPUT_GP, GPIO_OUT);
  gpio_put(TEST_OUTPUT_GP, 0);

  /*
   * For some reason the second core code doesn't get started after SWD programming
   * unless I pause for a moment here
   */
  busy_wait_us_32(100000);

  /* Init complete, run 2nd core code */
  multicore_launch_core1( core1_main ); 

  trace(TRC_CORE1_INIT, 0);

  /* Wait for the other core to initialise */
  while( core1_running == 0 );

  /*
   * This core responds to commands from the User Interface Pico. In theory it's
   * tightly controlled and "can't go wrong." In practise bytes might get lost
   * and the Picos get out of step during programming development. So at least
   * try to keep the communications in lockstep.
   */
  while( 1 )
  {
    /* Wait for IU Pico to say something */
    UI_TO_IO_CMD cmd = get_ui_to_io_cmd();

    /* ACK the command */
    send_ack_to_ui();

    switch( cmd )
    {
    case UI_TO_IO_INIALISE:
    {
      /* This doesn't do anything. The command is ACK'ed (above). */
    }
    break;

    case UI_TO_IO_TEST_LED_ON:
    {
      gpio_put(LED_PIN, 1);
    }
    break;
        
    case UI_TO_IO_TEST_LED_OFF:
    {
      gpio_put(LED_PIN, 0);
    }
    break;

    case UI_TO_IO_INSERT_MDR:
    {
      ui_to_io_insert_mdr_t cmd_struct;

      /* UI will respond with a structure describing the incoming MDR data */
      ui_link_receive_buffer( pio1, linkin_sm, linkout_sm, (uint8_t*)&cmd_struct, sizeof(cmd_struct) );
      send_ack_to_ui();

      // trace(TRC_RCV_INSERT_MDR_STRUCT, cmd_struct.microdrive_index);

      /*
       * There isn't enough room to store the whole 137KB image, so receive it in 256 byte pages.
       */
      bool     checksum_error = false;
      uint32_t pages = cmd_struct.data_size / 256;
      uint32_t final_page_size = cmd_struct.data_size - (pages * 256);
      for( uint32_t page=0; page < pages; page++ )
      {
        /* Load a page from the UI Pico into a local buffer */
        uint8_t page_buffer[ 256 ];
	ui_link_receive_buffer( pio1, linkin_sm, linkout_sm, page_buffer, sizeof(page_buffer) );

	uint16_t checksum;
	ui_link_receive_buffer( pio1, linkin_sm, linkout_sm, (uint8_t*)&checksum, 2 );

	if( fletcher16( page_buffer, 256 ) == checksum )
	{
	  /* Work out where to store this page in the PSRAM and write it in */
	  uint32_t psram_offset = (MICRODRIVE_CARTRIDGE_LENGTH * cmd_struct.microdrive_index)
                                   +
                                  (page*256);

	  write_psram_block( psram_offset, page_buffer, sizeof(page_buffer) );
	}
	else
	{
	  checksum_error = true;
	}
      }

      /* Do the last bit */
      if( final_page_size != 0 )
      {
        uint8_t page_buffer[ final_page_size ];
	ui_link_receive_buffer( pio1, linkin_sm, linkout_sm, page_buffer, sizeof(page_buffer) );

	uint16_t checksum;
	ui_link_receive_buffer( pio1, linkin_sm, linkout_sm, (uint8_t*)&checksum, 2 );

	if( fletcher16( page_buffer, final_page_size ) == checksum )
	{
	  uint32_t psram_offset = (MICRODRIVE_CARTRIDGE_LENGTH * cmd_struct.microdrive_index)
                                   +
                                  (pages*256);

	  write_psram_block( psram_offset, page_buffer, final_page_size );
	}
	else
	{
	  checksum_error = true;
	}
      }

      /*
       * If the file contents came over correctly, insert cartridge into microdrive.
       * Otherwise set the error flag, which will go back to the UI Pico in the
       * next status report
       */
      if( ! checksum_error )
      {
	/* Insert MDR image in PSRAM into the IF1 code so it can be accessed */
	cartridge_error_status[cmd_struct.microdrive_index] =
	                                 if1_mdr_insert( cmd_struct.microdrive_index,
							 MICRODRIVE_CARTRIDGE_LENGTH * cmd_struct.microdrive_index,
							 cmd_struct.data_size,
							 cmd_struct.write_protected );
      }
      else
      {
	/* Corruption in the UI->IO Pico transfer, this is unheard of in my testing */
	cartridge_error_status[cmd_struct.microdrive_index] = CARTRIDGE_ERR_CHECKSUM_INCORRECT;
      }
    }
    break;

    case UI_TO_IO_REQUEST_STATUS:
    {
      /* Command structure is currently a dummy, nothing is required */
      ui_to_io_request_status_t cmd_struct;
      ui_link_receive_buffer( pio1, linkin_sm, linkout_sm, (uint8_t*)&cmd_struct, sizeof(ui_to_io_request_status_t) );

      /* Loop over drives, tell the UI if each is inserted, needs saving, etc */
      io_to_ui_status_response_t status_response;
      for( uint8_t i=0; i < NUM_MICRODRIVES; i++ )
      {
	status_response.motor_on[i]        = is_mdr_motor_on( i );
	status_response.cartridge_error[i] = cartridge_error_status[i];

	if( is_cartridge_inserted(i) )
	{
	  if( is_cartridge_modified(i) )
	  {
	    status_response.status[i] = MD_STATUS_MDR_LOADED_NEEDS_SAVING;
	  }
	  else
	  {
	    status_response.status[i] = MD_STATUS_MDR_LOADED_UNCHANGED;
	  }
	}
	else
	{
	  if( is_cartridge_ejected_pending_save( i ) )
	  {
	    status_response.status[i] = MD_STATUS_MDR_EJECTED_NEEDS_SAVING;
	  }
	  else
	  {
	    status_response.status[i] = MD_STATUS_EMPTY;
	  }
	}
      }

      ui_link_send_buffer( pio1, linkout_sm, linkin_sm, (uint8_t*)&status_response, sizeof(io_to_ui_status_response_t) );
    }
    break;

    case UI_TO_IO_REQUEST_MDR_TO_SAVE:
    {
      /* UI Pico wants the contents of an inserted cartridge so it can save it back to SD card */
      ui_to_io_request_mdr_data_t cmd_struct;
      ui_link_receive_buffer( pio1, linkin_sm, linkout_sm, (uint8_t*)&cmd_struct, sizeof(ui_to_io_request_mdr_data_t) );
      
      /* Work out where in the psuedo RAM the microdrive's data is held */
      uint32_t psram_offset = (MICRODRIVE_CARTRIDGE_LENGTH * cmd_struct.microdrive_index);

      /*
       * Mark as no longer modified. This is done now, before the transfer to the UI Pico,
       * because the ZX could write to the image during the transfer. If it were to be
       * marked as "not modified" after the transfer, any modifications the ZX writes
       * during the transfer won't be marked as needing to be saved.
       *
       * If the cartridge has been ejected, but still requires its modified data to be saved
       * to SD card, it will have been marked as not inserted and no further writes can
       * have happened, nor will happen. So that flag can be cleared, and it's assumed that
       * when this data arrives back at the UI Pico the data will be safely stored on
       * the SD card.
       */
      set_cartridge_modified( cmd_struct.microdrive_index, false );
      set_cartridge_ejected_to_sd( cmd_struct.microdrive_index );

      /*
       * Send it page by page over to the UI Pico. The UI Pico controls the data size, it told us 
       * in the command structure how many bytes it's expecting
       */
      uint32_t pages = cmd_struct.bytes_expected / 256;
      uint32_t final_page_size = cmd_struct.bytes_expected - (pages * 256);
      for( uint32_t page=0; page < pages; page++ )
      {
        /* Load a page from the PSRAM device into a local buffer */
        uint8_t page_buffer[ 256 ];
	read_psram_block( psram_offset, page_buffer, 256 );

	/* Send it over to the UI Pico for saving to SD card */
	ui_link_send_buffer( pio1, linkout_sm, linkin_sm, page_buffer, sizeof(page_buffer) );

	/* Checksum for this 256 byte block */
	uint16_t checksum = fletcher16( page_buffer, sizeof(page_buffer) );
	ui_link_send_buffer( pio1, linkout_sm, linkin_sm, (uint8_t*)&checksum, 2 );

        /* Work out where the start of the next page is */
        psram_offset += 256;
      }

      if( final_page_size != 0 )
      {
	uint8_t page_buffer[final_page_size];
	read_psram_block( psram_offset, page_buffer, final_page_size );
	ui_link_send_buffer( pio1, linkout_sm, linkin_sm, page_buffer, sizeof(page_buffer) );

	uint16_t checksum = fletcher16( page_buffer, sizeof(page_buffer) );
	ui_link_send_buffer( pio1, linkout_sm, linkin_sm, (uint8_t*)&checksum, 2 );
      }

      /* I don't send back the w/p flag, the UI Pico already has that */

    }
    break;

    case UI_TO_IO_REQUEST_EJECT_MDR:
    {
      /* UI Pico wants a cartridge ejected */
      ui_to_io_request_eject_mdr_t cmd_struct;
      ui_link_receive_buffer( pio1, linkin_sm, linkout_sm, (uint8_t*)&cmd_struct, sizeof(ui_to_io_request_eject_mdr_t) );

blip_test_pin();      
      if1_mdr_eject( cmd_struct.microdrive_index );
blip_test_pin();      
    }
    break;

    default:
      blip_test_pin();      
      break;
    }

  } /* Infinite loop */

}



#if 0
/* Blip the result pin, shows on scope */
gpio_put( TEST_OUTPUT_GP, 1 );
__asm volatile ("nop");
__asm volatile ("nop");
__asm volatile ("nop");
__asm volatile ("nop");
gpio_put( TEST_OUTPUT_GP, 0 );
busy_wait_us_32(1);
#endif
